ARTS-Laboratory/Smart-Penetrometer-with-Edge-Computing-and-Intelligent-Embedded-Systems/SYS_DEV/Columbia/V0/V0.7/v0.7.0/sensors/software/README.md

# V0.6.2 Software Design

1. Collects electrical conductivity, ground temperature, ambient temperature, humidity, barometric pressure data, and ground velocity.
2. Stores data locally on microSD card.
3. Transmits data wirelessly to base station.

## [Return to V0.6.0](https://github.com/ARTS-Laboratory/Smart-Penetrometer-with-Edge-Computing-and-Intelligent-Embedded-Systems/blob/main/V0/V0.6/V0.6.0)
