ARTS-Laboratory/Smart-Penetrometer-with-Edge-Computing-and-Intelligent-Embedded-Systems/SYS_DEV/Columbia/V0/V0.7/v0.7.0/sensors/hardware/CAD/README.md

## CAD
1. CAD models for the package
1. Designed in Inventor and all models also provided as .stl and .step files as well.
1. Updated Solar cap to fit six solar cells and to improve assembly and waterproofing.
1. Split and modified body into two sections (base) to improve assembly and waterproofing.

### 1. Solar Cap
<p align="center">

</p>

### 2. body
<p align="center">

</p> 

### 3. plate
<p align="center">

</p>

### 4. base
<p align="center">

</p>

## [Return to V0.7.0](https://github.com/ARTS-Laboratory/Smart-Penetrometer-with-Edge-Computing-and-Intelligent-Embedded-Systems/tree/main/V0/V0.7/V0.7.0)
