ARTS-Laboratory/Smart-Penetrometer-with-Edge-Computing-and-Intelligent-Embedded-Systems/SYS_DEV/Columbia/V0/V0.5/V0.5.2/hardware_design/README.md

# Hardware Design
## [CAD](CAD)
### Fusion360 CAD models of sensor node structure

## [PCB](PCB)
### KiCad schematic, PCB, footprints, etc

## [Return to V0.5.2](https://github.com/ARTS-Laboratory/Smart-Penetrometer-with-Edge-Computing-and-Intelligent-Embedded-Systems/blob/main/V0/V0.5/V0.5.2)
