ARTS-Laboratory/Smart-Penetrometer-with-Edge-Computing-and-Intelligent-Embedded-Systems/SYS_DEV/Columbia/V0/V0.5/V0.5.2/hardware_design/CAD/README.md

## CAD
1. CAD models for the package
1. Designed in Fusion 360 and all models also provided as .stl files as well.
1. Updated Solar cap to screw into housing and added plugs for water resistance.
1. Removed Housing3 and modified Housing2.

### 1. Solar Cap
<p align="center">

</p>

### 2. Housing1
<p align="center">

</p>

### 3. Housing2
<p align="center">

</p>

## [Return to V0.5.2](https://github.com/ARTS-Laboratory/Smart-Penetrometer-with-Edge-Computing-and-Intelligent-Embedded-Systems/tree/main/V0/V0.5/V0.5.2)
