ARTS-Laboratory/Smart-Penetrometer-with-Edge-Computing-and-Intelligent-Embedded-Systems/SYS_DEV/Columbia/V0/V0.5/V0.5.1/hardware_design/PCB/README.md

## PCB
1. Designed footprint for VO615A optocoupler IC.
2. Updated schematic and PCB to include optocoupler, RTD circuit, and screw terminal for digital trigger with accompanying resistors and capacitors.
3. Added 3V3 voltage regulator to fix rf module power issues.
4. Added QR code that links to GitHub page.

<p align="center">

</p>

## [Return to V0.5.1](https://github.com/ARTS-Laboratory/Smart-Penetrometer-with-Edge-Computing-and-Intelligent-Embedded-Systems/edit/main/V0/V0.5/V0.5.1)
