ARTS-Laboratory/Smart-Penetrometer-with-Edge-Computing-and-Intelligent-Embedded-Systems/SYS_DEV/Columbia/V0/V0.4/V0.4.1/hardware_design/CAD/README.md

## CAD
1. CAD models for the package
1. Designed in Fusion 360 and all models also provided as .stl files as well.

### 1. Cap
<p align="center">

</p>

### 2. Housing
<p align="center">

</p>

### 3. Housing part 2
<p align="center">

</p>

## [Return to V0.3.0](https://github.com/ARTS-Laboratory/Smart-Penetrometers-with-Edge-Computing-and-Intelligent-Embedded-Systems/blob/main/V0/V0.3.0/hardware_design/README.md)
