ARTS-Laboratory/Smart-Penetrometer-with-Edge-Computing-and-Intelligent-Embedded-Systems/SYS_DEV/Columbia/V0/V0.3/V0.3.0/hardware_design/CAD/README.md

## CAD
### 1. Cap
1. Increased diameter of cap by 0.10mm.
2. Designed 2 holes for solar cell power wires to go through.

<p align="center">

</p>

### 2. Housing
1. Extended lenght of housing frame by 10mm.
2. Increased diameter of housing frame by 0.10mm.
3. Added slot for single cell battery.
4. Changed dimensions of PCB slot for new PCB.

<p align="center">

</p>

### 3. Housing part 2
1. Increased diameter of housing part 2 frame by 0.10mm.
2. Enlarged TDS sensor slot by 0.5mm.

<p align="center">

</p>

### 4. Solar cell attachment with fletching
<p align="center">

</p>

## [Return to V0.3.0](https://github.com/ARTS-Laboratory/Smart-Penetrometers-with-Edge-Computing-and-Intelligent-Embedded-Systems/blob/main/V0/V0.3.0/hardware_design/README.md)
