ARTS-Laboratory/Smart-Penetrometer-with-Edge-Computing-and-Intelligent-Embedded-Systems/SYS_DEV/Columbia/V0/V0.2/V0.2.0/hardware_design/PCB/README.md

## PCB
1.

<p align="center">

</p>

## [Return to V0.2.0 Readme](https://github.com/ARTS-Laboratory/Smart-Penetrometers-with-Edge-Computing-and-Intelligent-Embedded-Systems/blob/main/V0/V0.2.0/hardware_design/README.md)
