ARTS-Laboratory/Smart-Penetrometer-with-Edge-Computing-and-Intelligent-Embedded-Systems/SYS_DEV/Columbia/V0/V0.2/V0.2.0/hardware_design/CAD/README.md

## CAD
### 1. Cap

<p align="center">

</p>

### 2. Housing

<p align="center">

</p>

### 3. Housing part 2

<p align="center">

</p>

### 4. Solar cell attachment with fin hinges

<p align="center">

</p>

### 5. Hinge and pins

<p align="center">

</p>

## [Return to V0.2.0 Readme](https://github.com/ARTS-Laboratory/Smart-Penetrometers-with-Edge-Computing-and-Intelligent-Embedded-Systems/blob/main/V0/V0.2.0/hardware_design/README.md)
