ARTS-Laboratory/Smart-Penetrometer-with-Edge-Computing-and-Intelligent-Embedded-Systems/SYS_DEV/Columbia/V0/V0.1/V0.1.1/hardware_design/CAD/README.md

## CAD
### 1. Housing

### 2. Housing part 2

### 3. Cap

## [Return to V0.1.1 Readme](https://github.com/ARTS-Laboratory/Smart-Penetrometers-with-Edge-Computing-and-Intelligent-Embedded-Systems/tree/main/V0/V0.1.1/hardware_design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)
