ARTS-Laboratory/Smart-Penetrometer-with-Edge-Computing-and-Intelligent-Embedded-Systems/SYS_DEV/Columbia/V0/V0.1/V0.1.0/hardware_design/PCB/README.md

## PCB
### Capable of collecting data from geophone, accelerometer excluding freefall detection, tds sensor, and conductivity probe

## [Return to V0.1.0 Readme](https://github.com/ARTS-Laboratory/Smart-Penetrometers-with-Edge-Computing-and-Intelligent-Embedded-Systems/tree/main/V0/V0.1.0/hardware_design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)
