ARTS-Laboratory/Smart-Penetrometer-with-Edge-Computing-and-Intelligent-Embedded-Systems/SYS_DEV/Columbia/V0/V0.6/V0.6.0/sensor_node/hardware_design/PCB/smart penetrometer/smart penetrometer.step

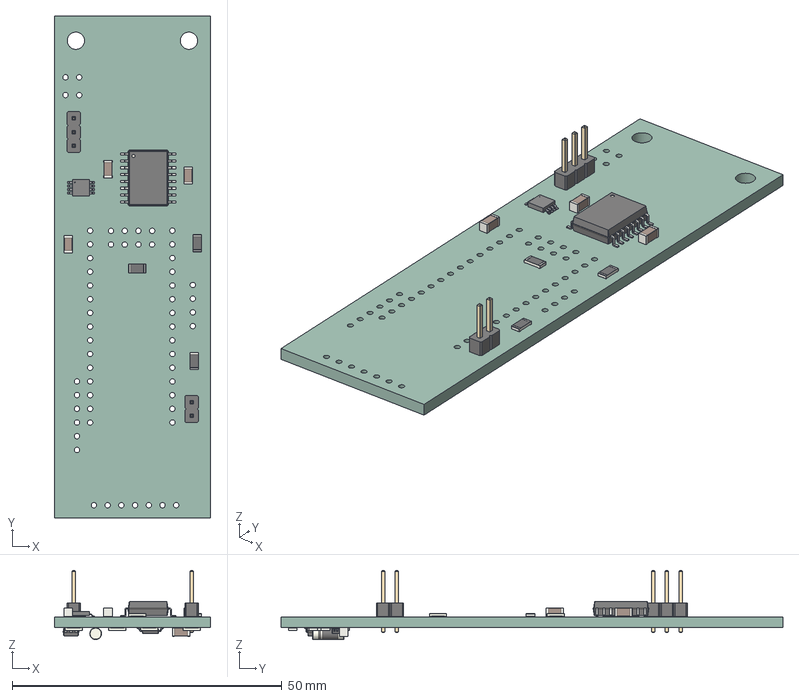
[picture p29: CAD file, 2024-04-03, an earlier design]
SYS_DEV/Columbia/V0/V0.6/V0.6.0/sensor_node/hardware_design/PCB/smart penetrometer/smart penetrometer.step
29.0 x 93.0 x 12.8 mm
smart penetrometer PCB
