ARTS-Laboratory/Smart-Penetrometer-with-Edge-Computing-and-Intelligent-Embedded-Systems/SYS_DEV/Columbia/V0/V0.5/V0.5.0/hardware_design/PCB/smart penetrometer/smart penetrometer.kicad_pcb

## KiCad design SYS_DEV/Columbia/V0/V0.5/V0.5.0/hardware_design/PCB/smart penetrometer/smart penetrometer.kicad_pcb (2023-07-24, an earlier design)

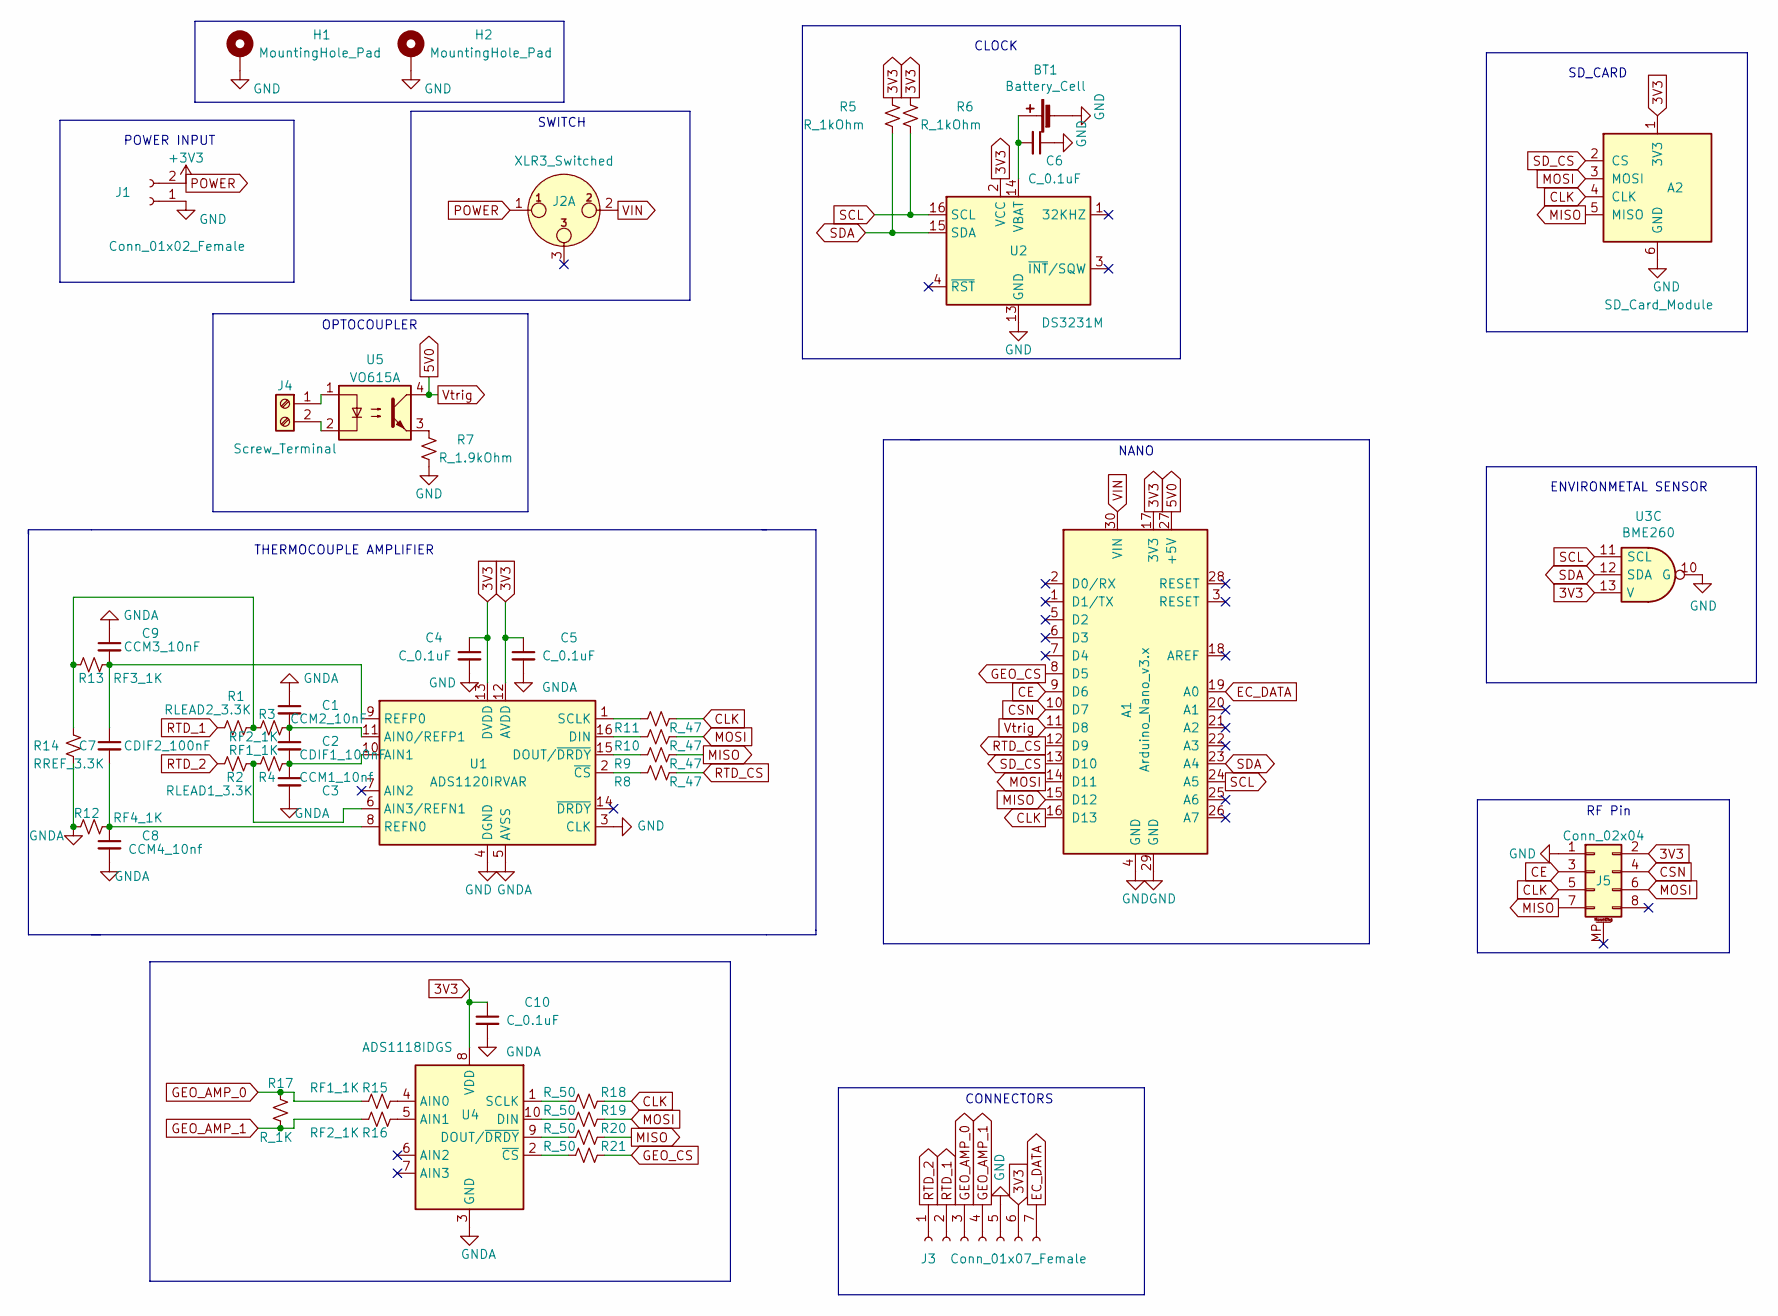
[picture p47: schematic smart penetrometer.kicad_sch, PENETROMETER BOARD]

Parts:
A1: Arduino_Nano_v3.x; Arduino_Nano
A2: SD_Card_Module; SD Module
BT1: Battery_Cell; battery_holder_10mm
C1: CCM2_10nF; C_1206_3216Metric
C2: CDIF1_100nF; C_1206_3216Metric
C3: CCM1_10nf; C_1206_3216Metric
C4, C5, C6, C10: C_0.1uF; C_1206_3216Metric
C7: CDIF2_100nF; C_1206_3216Metric
C8: CCM4_10nf; C_1206_3216Metric
C9: CCM3_10nF; C_1206_3216Metric
H1, H2: MountingHole_Pad; MountingHole_3.2mm_M3_Pad
J1: Conn_01x02_Female; PinSocket_1x02_P2.54mm_Horizontal
J2: XLR3_Switched; grounded_switch
J3: Conn_01x07_Female; PinSocket_1x07_P2.54mm_Horizontal
J4: Screw_Terminal; TerminalBlock_bornier-2_P5.08mm
J5: Conn_02x04; PinSocket_2x04_P2.54mm_Vertical
R1: RLEAD2_3.3K; R_1206_3216Metric
R2: RLEAD1_3.3K; R_1206_3216Metric
R3, R16: RF2_1K; R_1206_3216Metric
R4, R15: RF1_1K; R_1206_3216Metric
R5, R6: R_1kOhm; R_1206_3216Metric
R7: R_1.9kOhm; R_1206_3216Metric
R8, R9, R10, R11: R_47; R_1206_3216Metric
R12: RF4_1K; R_1206_3216Metric
R13: RF3_1K; R_1206_3216Metric
R14: RREF_3.3K; R_1206_3216Metric
R17: R_1K; R_1206_3216Metric
R18, R19, R20, R21: R_50; R_1206_3216Metric
U1: ADS1120IRVAR; ADS1120IPW 16TSSOP
U2: DS3231M; SOIC-16W_7.5x10.3mm_P1.27mm
U3: BME260; TDS_module
U4: ADS1118IDGS; ADS1118_10VSSOP
U5: VO615A; Vishay_VOS615A

Connections:
3V3: A1.17 (3V3), A2.1 (3V3), C4.1, C5.1, C10.1, J3.6, J5.2, R5.1, R6.1, U1.12 (AVDD), U1.13 (DVDD), U2.2 (VCC), U3.13, U4.8 (VDD)
5V0: A1.11 (D8), A1.27 (+5V), U5.4
CE: A1.9 (D6), J5.3
CLK: A1.16 (D13), A2.4 (CLK), J5.5, R11.1, R18.1
CSN: A1.10 (D7), J5.4
EC_DATA: A1.19 (A0), J3.7
GEO_AMP_0: J3.3, R15.2, R17.1
GEO_AMP_1: J3.4, R16.2, R17.2
GEO_CS: A1.8 (D5), R21.1
MISO: A1.15 (D12), A2.5 (MISO), J5.7, R9.1, R20.1
MOSI: A1.14 (D11), A2.3 (MOSI), J5.6, R10.1, R19.1
unnamed: BT1.1 (+), C6.2, U2.14 (VBAT)
unnamed: J4.1, U5.1
unnamed: J4.2, U5.2
unnamed: R1.1, R3.2, R13.1, R14.2
unnamed: R7.1, U5.3
unnamed: C1.2, C2.1, R3.1, U1.11 (AIN0/REFP1)
unnamed: C2.2, C3.1, R4.1, U1.10 (AIN1)
unnamed: R2.2, R4.2, U1.6 (AIN3/REFN1)
unnamed: R10.2, U1.16 (DIN)
unnamed: R9.2, U1.15 (DOUT/~DRDY)
unnamed: C7.2, C8.1, R12.2, U1.8 (REFN0)
unnamed: C7.1, C9.2, R13.2, U1.9 (REFP0)
unnamed: R11.2, U1.1 (SCLK)
unnamed: R8.2, U1.2 (~CS)
unnamed: R15.1, U4.4 (AIN0)
unnamed: R16.1, U4.5 (AIN1)
unnamed: R19.2, U4.10 (DIN)
unnamed: R20.2, U4.9 (DOUT/~DRDY)
unnamed: R18.2, U4.1 (SCLK)
unnamed: R21.2, U4.2 (~CS)
POWER: J1.2, J2.1
RTD_1: J3.2, R1.2
RTD_2: J3.1, R2.1
RTD_CS: A1.12 (D9), R8.1
SCL: A1.24 (A5), R6.2, U2.16 (SCL), U3.11
SDA: A1.23 (A4), R5.2, U2.15 (SDA), U3.12
SD_CS: A1.13 (D10), A2.2 (CS)
VIN: A1.30 (VIN), J2.2

Notes on the sheet:
THERMOCOUPLE AMPLIFIER
POWER INPUT
NANO
SWITCH
CLOCK
RF Pin
CONNECTORS
SD_CARD
ENVIRONMETAL SENSOR
OPTOCOUPLER

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
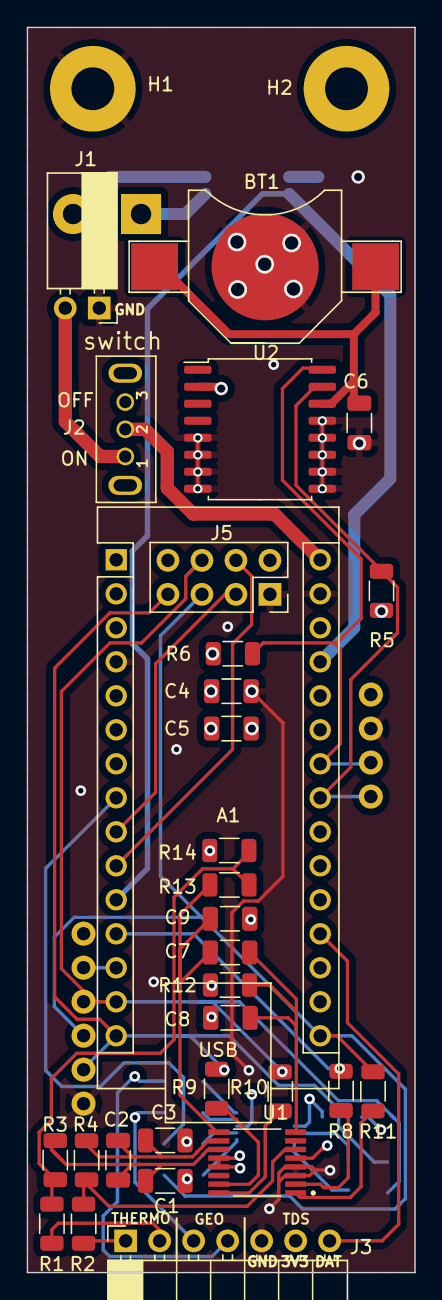
[picture p48: board SYS_DEV/Columbia/V0/V0.5/V0.5.0/hardware_design/PCB/smart penetromete… from above]

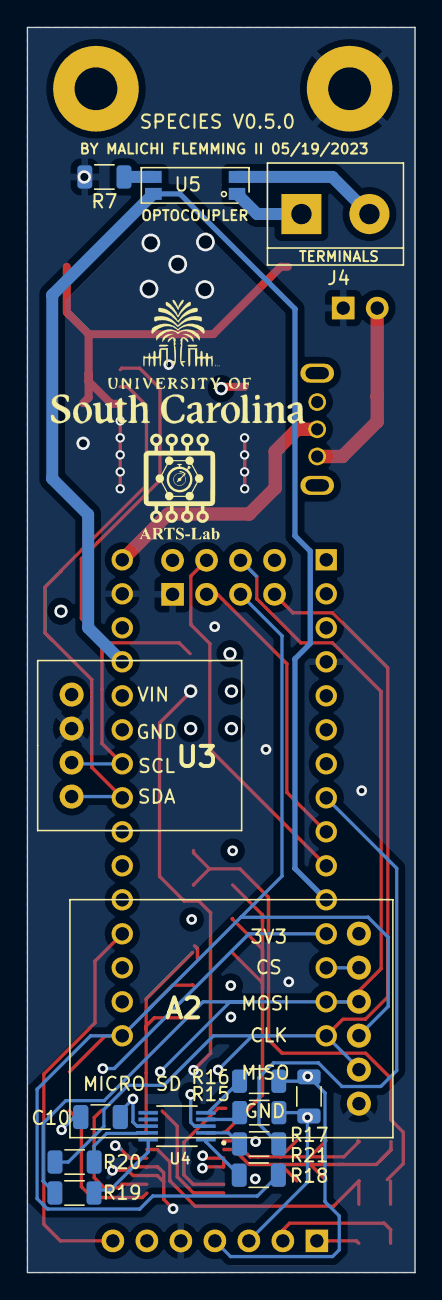
[picture p49: board SYS_DEV/Columbia/V0/V0.5/V0.5.0/hardware_design/PCB/smart penetromete… from below]

Board: 4 copper layers, 29.0 x 93.0 mm, 46 parts (14 on the bottom side), 41 nets.
